JuanRodriguez19/JnJ-s-Clockwork/Documentation/Pictures/Top View.jpg

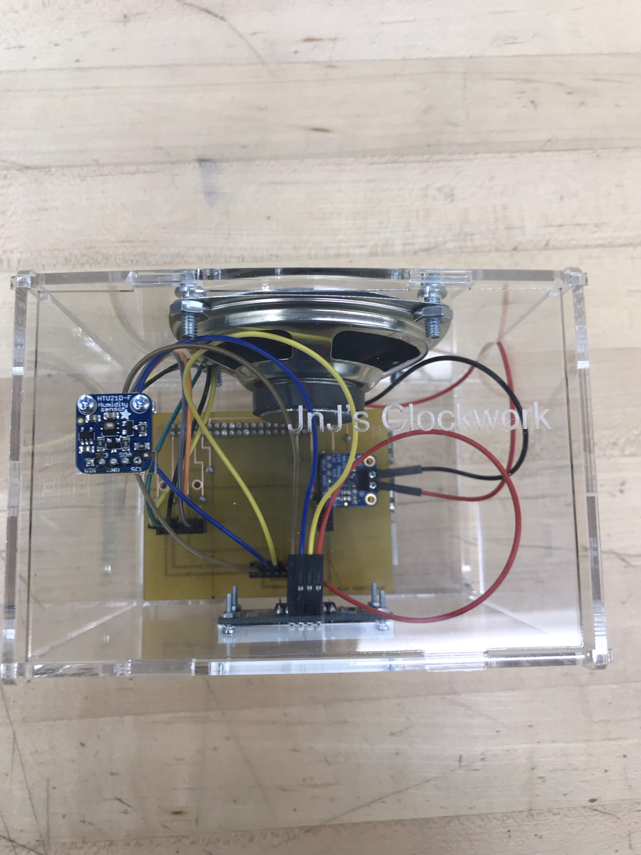
Documentation/Pictures/Top View.jpg
